SylvainVanIniitu/Piccolo-4C-Black/src/transfoAffichage.h

// void affichage () {}
// sera effacée TODO DEBUG ****

// PROTOTYPE
String GiveNameOfMode(int NNN);
int plusGrandNombreAvecAbits(int a);
String GiveNameOfModeShort(int NNN);

// FC
void affichageLine1()
{

    int potVal2;
    potVal2 = softwareValueEncoderRight;

    switch (Transfo[softwareValueEncoderLeft][0])
    {

        // NOTE**** on peut remplacer quasi tous les printRotFast par un PrintRotFast qui va afficher les noms
        // sauf pour certaines exceptions

    case 14: // CH+Time Info     // ajouter MUTE info
    {

        affiche = String(layerChannel[0] + 1); // attention, le layerChannel n'est pas forcéement le channel de toutes les notes du layer !
        affiche += (F(":"));                   // layerChannel est codé en MIDI hardware : 0 = CHANNEL 1
        affiche += String(layerLength[0]);
        affiche += (F(" "));
        buffer_setCursor(0, 0);
        buffer_print(affiche);

        affiche = String(layerChannel[2] + 1); // attention, le layerChannel n'est pas forcéement le channel de toutes les notes du layer !
        affiche += (F(":"));                   // layerChannel est codé en MIDI hardware : 0 = CHANNEL 1
        affiche += String(layerLength[2]);
        affiche += (F(" "));
        buffer_setCursor(8, 0);
        buffer_print(affiche);

        affiche = String(layerChannel[1] + 1); // attention, le layerChannel n'est pas forcéement le channel de toutes les notes du layer !
        affiche += (F(":"));                   // layerChannel est codé en MIDI hardware : 0 = CHANNEL 1
        affiche += String(layerLength[1]);
        affiche += (F(" "));
        buffer_setCursor(0, 1);
        buffer_print(affiche);

        affiche = String(layerChannel[3] + 1); // attention, le layerChannel n'est pas forcéement le channel de toutes les notes du layer !
        affiche += (F(":"));                   // layerChannel est codé en MIDI hardware : 0 = CHANNEL 1
        affiche += String(layerLength[3]);
        affiche += (F(" "));
        buffer_setCursor(8, 1);
        buffer_print(affiche);
    }
    break;

    case 30:
    { // EYE CANDY
    }
    break;

    case 46: // CH+Ratio Info     // ajouter MUTE info
    {

        affiche = String(layerChannel[0] + 1); // attention, le layerChannel n'est pas forcéement le channel de toutes les notes du layer !
        affiche += (F(":"));                   // layerChannel est codé en MIDI hardware : 0 = CHANNEL 1
        affiche += String(ratioLength[0]);
        affiche += (F(" "));
        buffer_setCursor(0, 0);
        buffer_print(affiche);

        affiche = String(layerChannel[2] + 1); // attention, le layerChannel n'est pas forcéement le channel de toutes les notes du layer !
        affiche += (F(":"));                   // layerChannel est codé en MIDI hardware : 0 = CHANNEL 1
        affiche += String(ratioLength[2]);
        affiche += (F(" "));
        buffer_setCursor(8, 0);
        buffer_print(affiche);

        affiche = String(layerChannel[1] + 1); // attention, le layerChannel n'est pas forcéement le channel de toutes les notes du layer !
        affiche += (F(":"));                   // layerChannel est codé en MIDI hardware : 0 = CHANNEL 1
        affiche += String(ratioLength[1]);
        affiche += (F(" "));
        buffer_setCursor(0, 1);
        buffer_print(affiche);

        affiche = String(layerChannel[3] + 1); // attention, le layerChannel n'est pas forcéement le channel de toutes les notes du layer !
        affiche += (F(":"));                   // layerChannel est codé en MIDI hardware : 0 = CHANNEL 1
        affiche += String(ratioLength[3]);
        affiche += (F(" "));
        buffer_setCursor(8, 1);
        buffer_print(affiche);
    }
    break;



    case 48: // CH+Fidelity Info     //
    {

        affiche = String(layerChannel[0] + 1); // attention, le layerChannel n'est pas forcéement le channel de toutes les notes du layer !
        affiche += (F(":"));                   // layerChannel est codé en MIDI hardware : 0 = CHANNEL 1
        affiche += String(fidelityLayer_[0]);
        affiche += (F(" "));
        buffer_setCursor(0, 0);
        buffer_print(affiche);

        affiche = String(layerChannel[2] + 1); // attention, le layerChannel n'est pas forcéement le channel de toutes les notes du layer !
        affiche += (F(":"));                   // layerChannel est codé en MIDI hardware : 0 = CHANNEL 1
        affiche += String(fidelityLayer_[2]);
        affiche += (F(" "));
        buffer_setCursor(8, 0);
        buffer_print(affiche);

        affiche = String(layerChannel[1] + 1); // attention, le layerChannel n'est pas forcéement le channel de toutes les notes du layer !
        affiche += (F(":"));                   // layerChannel est codé en MIDI hardware : 0 = CHANNEL 1
        affiche += String(fidelityLayer_[1]);
        affiche += (F(" "));
        buffer_setCursor(0, 1);
        buffer_print(affiche);

        affiche = String(layerChannel[3] + 1); // attention, le layerChannel n'est pas forcéement le channel de toutes les notes du layer !
        affiche += (F(":"));                   // layerChannel est codé en MIDI hardware : 0 = CHANNEL 1
        affiche += String(fidelityLayer_[3]);
        affiche += (F(" "));
        buffer_setCursor(8, 1);
        buffer_print(affiche);
    }
    break;

    case 82:
    {
        // TODO DEBUG  à modifier de façon plus jolie !
        currentFileNumber = softwareValueEncoderRight;

        if (SDCardPresente == true)
        {
            NameTransfo = F("Load Nr");
            NameTransfo += String(currentFileNumber);
            printRot2(NameTransfo, 11, 400, 2);
        }
        else
        {
            affiche = "NO SD";
            printRot2(affiche, 11, 400, 2);
        }
    }
    break;

        /* DISMISS 2C27 

    case 84:
    {
        currentFileNumber = softwareValueEncoderRight;

        if (SDCardPresente)
        {
            NameTransfo = F("PLAY MIDI#");
            NameTransfo += String(currentFileNumber);
            printRot2(NameTransfo, 11, 400, 2);
        }
        else
        {
            affiche = "NO SD";
            printRot2(affiche, 11, 400, 2);
        }

        // NameFileNumber(currentFileNumber) ;
        // printRot2(name,10,400,3);
        // midiname = name ;

        // print(F("PLAY MIDI#"));
        // print(currentFileNumber);
        // .print(F("   "));
        // u.setCursor(0, 1);
        // NameFileNumber(currentFileNumber) ;
        // .print(name);
        // midiname = name ;
    }
    break;
*/

    case 93:
    {
        currentFileNumber = softwareValueEncoderRight;

        if (SDCardPresente)
        {
            NameTransfo = F(">LOAD MIDI#");
            NameTransfo += String(currentFileNumber);
            printRot2(NameTransfo, 11, 400, 2);
        }
        else
        {
            printRot2("NO SD", 11, 400, 2);
        }
    }
    break;

    case 111:
    {
        affiche = PiccoloVersion;
        printRot2(affiche, 10, 300, 2);
    }
    break;

    case 126: // Define Which
    {
        switch (Evenement[CurrentEvenement].type)
        {
        case (1):
        {
            printRot2(F("Select CC"), 11, 400, 2);
        }
        break;

        case (2):
        {
            printRot2(F("Select Transfo"), 11, 400, 2);
        }
        break;
        default:
        {
            printRot2(F("Select Type first !"), 11, 400, 2);
        }
        break;
        }
    }
    break;

    case 134:
    {
        // Define Value

        if (Evenement[CurrentEvenement].type == 1)
        {
            printRot2(F(">Select Value to send to CC"), 11, 400, 2);
        }

        if (Evenement[CurrentEvenement].type == 2)
        {
            printRot2(F(">Select Transfo VALUE"), 11, 400, 2);
            // // old potVal2 mapping ;
            // // old potVal2 mapping ;

            // d'abord déterminer quelle est la transfo actuellement envisagée
            // ensuite savoir quelle ligne du tableau Transfo appelle cette Transformation
            // ensuite faire un mapping entre potVal2 et les valeurs données par Transfo !

            // potVal2 = map(potVal2, 0, 1023, Transfo[LineCallingTransfo(Evenement[CurrentEvenement].which)][1], Transfo[LineCallingTransfo(Evenement[CurrentEvenement].which)][2] ) ;

            // dans un premier temps on peut afficher la valeur telle que modifiée par le tableau TRANSFO
            // pour la Transformation[Which]
            // dans second temps il faut viser affichage comme dans le browser habituel

            // String affiche ;
            // affiche = "Send " + String(potVal2) + " to Transfo" + String(Evenement[CurrentEvenement].which) ;
            // printRot2(affiche,10,400,3  );

            // NOTE **** On doit ici compléter par le nom de la transformation
        }
    }
    break;

    case 163:
    { // view Channel direction
        // // old potVal2 mapping ;
        // // old potVal2 mapping ;

        // GetNameTransformation( softwareValueEncoderRight );
        NameTransfo = "CH" + String(potVal2);
        printRot2(NameTransfo, 11, 400, 2);

        //buffer_and_HARD_setCursor(0, 1);
        //printMatrixLine(midiRedirect,potVal2-1);
    }
    break;

    case 246: // layer Counters
    {

        affiche = "1:"; // attention, le layerChannel n'est pas forcéement le channel de toutes les notes du layer !
        affiche += String(layerCounter[0]);
        affiche += (F(" "));
        buffer_setCursor(0, 0);
        buffer_print(affiche);

        affiche = "3:"; // attention, le layerChannel n'est pas forcéement le channel de toutes les notes du layer !
        affiche += String(layerCounter[2]);
        affiche += (F(" "));
        buffer_setCursor(8, 0);
        buffer_print(affiche);

        affiche = "2:"; // attention, le layerChannel n'est pas forcéement le channel de toutes les notes du layer !
        affiche += String(layerCounter[1]);
        affiche += (F(" "));
        buffer_setCursor(0, 1);
        buffer_print(affiche);

        affiche = "4:"; // attention, le layerChannel n'est pas forcéement le channel de toutes les notes du layer !
        affiche += String(layerCounter[3]);
        affiche += (F(" "));
        buffer_setCursor(8, 1);
        buffer_print(affiche);
    }
    break;

    case 373:
    {
        // TODO DEBUG  à modifier de façon plus jolie !
        currentFileNumber = softwareValueEncoderRight;

        if (SDCardPresente == true)
        {
            NameTransfo = F("Load Nr");
            NameTransfo += String(currentFileNumber);
            printRot2(NameTransfo, 11, 400, 2);
        }
        else
        {
            affiche = "NO SD";
            printRot2(affiche, 11, 400, 2);
        }
    }
    break;

    case 508:
    {
        // TODO DEBUG  à modifier de façon plus jolie !
        currentFileNumber = softwareValueEncoderRight;

        if (SDCardPresente == true)
        {
            NameTransfo = F("K_Load Nr");
            NameTransfo += String(currentFileNumber);
            printRot2(NameTransfo, 11, 400, 2);
        }
        else
        {
            affiche = "NO SD";
            printRot2(affiche, 11, 400, 2);
        }
    }
    break;

    default:
    {
        GetNameTransformation(Transfo[softwareValueEncoderLeft][0]);
        printRot2(NameTransfo, 12, 400, 2);
    }
    break;

    } // end of switch avec toutes les valeurs de Transformatiosn

} // fin de la procédure affichage Line 1

void affichageLine2(int thisTransfo)
{
    int potVal2;
    potVal2 = softwareValueEncoderRight;

    busyWithMIDIAffichage = false; // il faut veiller qd on sort de 218 à passer au moins 1x par l'affichage de 217
    // pour toutes les fois où on n'est pas dans 218, fait que cette valeur est fausse
    // NOTE DEBUG je n'ai pas trouvé de moyen plus court pour dire qd on n'est pas dans une fc qui rend cette valeur vraie
    //
    // switch ( Transfo[softwareValueEncoderLeft][0] ) {
    switch (thisTransfo)
    {
        // NOTE**** on peut remplacer quasi tous les printRotFast par un PrintRotFast qui va afficher les noms
        // sauf pour certaines exceptions

    case 6:
    {
        // potVal2 = analogRead(A1);

        switch (potVal2)
        {
        case 1:
            potVal2 = 1;
            break;
        case 2:
            potVal2 = 10;
            break;
        case 3:
            potVal2 = 100;
            break;
        case 4:
            potVal2 = 1000;
            break;
        case 5:
            potVal2 = 10000; // soit 10 secondes            break;
        }

        String affiche;
        affiche = String(potVal2) + F(" msec ");
        printRot2(affiche, 16, 400, 3);
    }
    break;

    case 11:
    { // MULTIPLY

        int potVal3 = (softwareValueEncoderRight / 7) + 1;
        potVal2 = (softwareValueEncoderRight % 7) + 1;

        String affiche;
        affiche = String(potVal2) + F("/") + String(potVal3) + F(" ");
        printRot2(affiche, 16, 400, 3);
    }
    break;

    case 12:
    { // Meltiply

        int potVal3 = (softwareValueEncoderRight / 7) + 1;
        potVal2 = (softwareValueEncoderRight % 7) + 1;

        String affiche;
        affiche = String(potVal2) + F("/") + String(potVal3) + F(" ");
        printRot2(affiche, 16, 400, 3);
    }
    break;

    case 14: // CH+Time Info     // ajouter MUTE info
    {
    }
    break;

    case 20:
    {
        // printRotFast(F("(un)MUTE"));
        //
        // TODO transformer en String et PrintRot2 ****

        affiche = nulString;
        ;
        for (byte i = 0; i < nbLayer; i++)
        {
            // déterminer si la layer i est mute
            // déterminer si la layer i est mute
            byte k = ((muteLayer >> i) & B00000001); // le bit de droite est 1 si layer 0 est MUTE ; le 2ème bit est 1 si layer 1 est MUTE, etc...
            if (k == B00000001)
            {
                affiche += F("M");
            }
            else
            {
                affiche += (F("-"));
            }
        }
        printRot2(affiche, 16, 300, 3);
    };
    break;

    case 23:
    { // AUTO FX

        affiche = nulString;
        if (automodification == true)
        {
            affiche = F(" ON ");
        }
        else
        {
            affiche = F("OFF");
        }

  
        // // old potVal2 mapping ;
        // potVal2 = map(potVal2, 0, 1023, Transfo[softwareValueEncoderLeft][1] , Transfo[softwareValueEncoderLeft][2] + 1); // dépendra de l'effet choisi.

        affiche = affiche + String(potVal2) + F(" sec");
        printRot2(affiche, 16, 400, 3);
    }

    break;

    case 24:
    { // RECORD ON/OFF
        printRot2(record == true ? F("ON ") : F("OFF"), 16, 300, 3);
    }
    break;

    case 25: // MIDIOx MIDI Ox
    {

        // MODIF 2C18 KANNIBAL 2 !!!
        // on enlève le .Read direct, pour se fier à la dernière valeur enrgistrée !
        // 2C19 on enlève l'affichage F8 !

        // byte note(0);
        // byte channel(0);
        // byte velocity(0);
        // String affiche;

        // if (MIDI3.read(0))
        // {
        //     channel = MIDI3.getChannel(); // donne le channel, pas le codage du channel ! CH1 = 0 pour machine
        //     note = MIDI3.getData1();
        //     velocity = MIDI3.getData2();
        //     timenote = nowMillis;
        // }

        // if ( note != 0 ) {
        switch (midiType)
        {
        case midi::NoteOn:
        {
            // digitalWrite(5, HIGH);

            affiche = F("CH");
            affiche += String(channel + 1); //2C28 affichage toujours humain, calculs toujours machine
            affiche = affiche + F("N");
            affiche = affiche + String(note);
            affiche = affiche + ".";
            affiche = affiche + String(velocity);
            printRot2(affiche, 16, 400, 3);

            //  digitalWrite(5, LOW);
        }
        break;

        case midi::NoteOff:
        {
            affiche = F("CH");
            affiche += String(channel + 1); // 2C28 affichage toujours humain, calcul toujours machine
            affiche = affiche + F("N");
            affiche = affiche + String(note);
            affiche = affiche + F("x");
            affiche = affiche + String(velocity);
            printRot2(affiche, 16, 400, 3);
        }
        break;

            // polyPressure            = 0x0A,
            //   56         controlChange           = 0x0B,
            //   57         programChange           = 0x0C,
            //   58         channelPressure         = 0x0D,
            //   59         pitchBend               = 0x0E,
            //
            //

        case midi::AfterTouchPoly:
        {
            affiche = F("PolyPressureCH");
            affiche += String(channel + 1);
            affiche = affiche + F("N");
            affiche = affiche + String(note);
            affiche = affiche + F(":");
            affiche = affiche + String(velocity);
            printRot2(affiche, 16, 400, 3);
        }
        break;

        case midi::ControlChange:
        {
            // if (channel != 0 && note != 0)
            if (note != 0)
            {
                affiche = F("/CC/ CH");
                affiche += String(channel + 1);
                affiche = affiche + F("V");
                affiche = affiche + String(note);
                affiche = affiche + F(":");
                affiche = affiche + String(velocity);
                affiche += F(" ");
                printRot2(affiche, 16, 400, 3);
            }
        }
        break;

        case midi::ProgramChange:
        {
            affiche = F("*PC* CH");
            affiche += String(channel + 1);
            affiche = affiche + F("V");
            affiche = affiche + String(note);
            affiche = affiche + F(":");
            affiche = affiche + String(velocity);
            printRot2(affiche, 16, 400, 3);
        }
        break;

        case midi::PitchBend:
        {
            affiche = F("Bend CH");
            affiche += String(channel + 1);
            affiche = affiche + F("V");
            affiche = affiche + String(note);
            affiche = affiche + F(":");
            affiche = affiche + String(velocity);
            printRot2(affiche, 16, 400, 3);
        }
        break;

        default:
            if (midiType != 248)
            {
                affiche = String(midiType);
                affiche += "/";
                affiche += String(channel + 1);
                affiche = affiche + F("?");
                affiche = affiche + String(note);
                affiche = affiche + F("?");
                affiche = affiche + String(velocity);
                printRot2(affiche, 16, 400, 3);

                break;
            }
        }
        // }
    }
    break;

    case 26:
    {
        // premier de la deuxième ligne à bénéficier de printRot2

        // String affiche ;
        affiche = "1 iter = ";
        affiche += String((int)currentCounterSpeed);
        // affiche += "->";
        // affiche += String((int)meancounterspeed);
        // affiche = affiche + F(" microsec  ");
        //  Rfirsttime[3] = true ; // va forcer l'affichage mis à jour
        printRot2(affiche, 16, 400, 3);
    }
    break;

    case 30:
    { // EYE CANDY
        // buffer_and_HARD_setCursor(random(0, 16), random(0, 2));
        // buffer_and_HARD_print((char)random(33, 255));
        // montrer particulièrement la lenteur d'un écran !!!
    }
    break;

    case 31:
    { // ACTIVE LAYER CHOOSER

        affiche = nulString;

        for (byte i = 0; i < nbLayer; i++)
        {
            // déterminer si la layer i est active
            byte k = ((((byte)potVal2) >> i) & B00000001); // le bit de droite est 1 si layer 0 est ON ; le 2ème bit est 1 si layer 1 est ON, etc...
            if (k == B00000001)
            {
                affiche += String(i + 1);
            }
            else
            {
                affiche += "-";
            }
        }

        printRot2(affiche, 16, 400, 3);
    }
    break;

        /////////////////////////////////////////////////////////////////////////////////////
        // PILE VERSION : faite et vérifiée
        // 1C94
        /////////////////////////////////////////////////////////////////////////////////////

    case 32:
    {
        // FIRST FREEnote

        affiche = nulString;
        ;

        for (byte i = 0; i < nbLayer; i++)
        {
            affiche += String(mesureTaillePileComplete(pInitial[i]));
            // if (anyFreeNote(i))
            // {
            //     affiche += String(firstfreenote(i));
            // }
            // else
            // {
            //     affiche += F("R");
            // }
            affiche += F(".");
        }

        printRot2(affiche, 16, 400, 3);
    };
    break;

    case 35:
    {
        // MIRROR
        // va devoir indiquer le nb de notes présentes avant ce % là des layers

        affiche = nulString;
        affiche += String(potVal2);
        affiche += F("% = ");

        unsigned long foldtime;
        long calcultime; // doit parfois être négatif !!!!
        int total = 0;

        for (byte i = 0; i < nbLayer; i++)
        {

            if (isLayerActive(i))
            {

                calcultime = (((long)layerLength[i] * (long)potVal2) / (long)100);
                foldtime = (signed int)(calcultime);
                // on doit pouvoir se passer de la variable foldtime en fait !
                // affiche+=String(foldtime);

                //1C97
                unsigned int taille = mesureTaillePileComplete(pInitial[i]);
                pileNote tempNote;

                for (byte j = 0; j < taille; j++)
                { //
                    tempNote = ZEROgetNoteFromPile(pInitial[i], j);

                    if ((tempNote.note != 0) && (tempNote.startNote < foldtime))
                    {
                        total++;
                    }
                }
            }
        }

        affiche += String(total);
        affiche += F(" notes");

        printRot2(affiche, 16, 400, 3);
    };
    break;

    case 39:
    { // Velocity

        if (potVal2 < 127)
        {
            affiche = String(potVal2) + " ";
        }
        else
        {
            affiche = F("RND");
        }
        printRot2(affiche, 16, 400, 3);
    }
    break;

    case 40: // HARMONIZE
    {
        //2C19 modification radicale : gamme pour chaque layer

        affiche = nulString;
        // 2C12 va afficher le gamme du layer 1 et transforme tout d'un coup

        // 2C28 : va de C à C et plus de C à F comme avant !

        for (byte i = 0; i < nbLayer; i++)
        {
            if (isLayerActive(i))
            {
                affiche += GiveNameOfNote(potVal2);
                affiche += " ";
            }
            else
            {
                affiche += (GiveNameOfNote(gammeActuelle[i]));
                affiche += " ";
            }
        }

        printRot2(affiche, 16, 400, 3);
    }
    break;

    case 41: // ROOT NOTE
    {
        // 2C12 va afficher le gamme du layer 1 et transforme tout d'un coup

        // 2C27
        affiche = GiveNameOfNote(potVal2);
        affiche += flechedroite;

        for (byte i = 0; i < nbLayer; i++)
        {
            // if (isLayerActive(i))
            //  {
            //     affiche += GiveNameOfNote(potVal2);
            //     affiche += " ";
            // }
            // else
            {
                affiche += (GiveNameOfNote(gammeActuelle[i]));
                affiche += " ";
            }
        }

        printRot2(affiche, 16, 400, 3);
    }
    break;

    case 42:
    { // affichage du Record MODE
        affiche = nulString;
        ;

        // potVal2 = analogRead(A1);
        // old potVal2 mapping ;
        // old potVal2 mapping ;

        switch (potVal2)
        {
        case 0:
            affiche += (F("1.REC 2 LAYER CH"));
            break;
        case 1:
            affiche += (F("2.REC + SOURCE CH"));
            break; // par défaut
        case 2:
            affiche += (F("3.REC - CH        "));
            break;
        default:
            affiche += (F("oink"));
            break;
        }
        printRot2(affiche, 16, 400, 3);
    }
    break;

    case 45:
    {
        // old potVal2 mapping ;
        // old potVal2 mapping ;

        affiche = nulString;

        affiche = String(potVal2);
        affiche += F("%  ");

        // TODO fonction qui remplace ceci : va combler String jusque 8

        switch (varispeedState)
        {
        case 1:
            affiche += (F("  OFF"));
            break;
        case 2:
        {
            affiche += (F("  ON!"));

            for (byte i = 0; i < nbLayer; i++)
            {
                if (isLayerActive(i))
                {
                    ratioCurrent[i] = potVal2; //
                }
            }
        }
        break;
        case 3:
            affiche += (F("  FIX"));
            break;
        case 4:
            affiche += (F("  MOD"));
            break;
        default:
            affiche += (F("  ???"));
            break;
        }
        printRot2(affiche, 16, 400, 3);
    }
    break;

    case 46:
    { // CH+Ratio Info     // ajouter MUTE info
    }
    break;

    case 47: // Fidelity Black10
    {
affiche = nulString ; 
// affiche += potVal2 ;
affiche += afficheValueStraightOrFromSequence(potVal2, "%", 0);
affiche += ">"; 

        for (byte i = 0; i < nbLayer; i++)
        {
            affiche += afficheValueStraightOrFromSequence(fidelityLayer_[i], "%", 0);
            affiche += " "; 
        }
        printRot2(affiche, 16, 400, 3);
      }
    break;

    case 48:
    { // CH+Fidelity Info     //
    }
    break;

    case 50: // Tabula Rasa
    {

        affiche = nulString;
        ;

        // potVal2 = analogRead(A1);
        // old potVal2 mapping ;
        // old potVal2 mapping ;

        switch (potVal2)
        {
        case 0:
            affiche += (F("0??      "));
            break;
        case 1:
            affiche += (F("Pyramid  "));
            break;
        case 2:
            affiche += (F("Square   "));
            break;
        case 3:
            affiche += (F("Random   "));
            break;
        case 4:
            affiche += (F("Complex  "));
            break;
        case 5:
            affiche += (F("Long 32  "));
            break;
        case 6:
            affiche += (F("SlaveRave"));
            break;
        case 7:
            affiche += (F("Technoid4"));
            break;
        case 8:
            affiche += (F("5/5/3   "));
            break;
        case 9:
            affiche += (F("3/5/3    "));
            break;
        default:
            affiche += (F("--------- "));
            break;
        }
        printRot2(affiche, 16, 400, 3);
    };
    break;

    case 51:
    {

        affiche = nulString;
        ;

        //        potVal2 = analogRead(A1);
        // old potVal2 mapping ;
        // old potVal2 mapping ;
        if (potVal2 < 17)
        {
            affiche = String(potVal2); // le CH MIDI est la valeur +1
        }
        else
        {
            switch (potVal2)
            {
            case 17:
                affiche = F("idem");
            case 18:
                affiche = F("OFF ");
            default:
                break;
            }
        }
        printRot2(affiche, 16, 400, 3);
    };
    break;

    case 58:
    { // FUNKY VEL   FunkyVel FunkyVelValue
        affiche = nulString;

        affiche = String(potVal2);
        affiche += F(" ");

        if (FunkyVel == true)
        {
            affiche += (F("ON  "));
        }
        else
        {
            affiche += (F("OFF "));
        }

        for (byte i = 0; i < nbLayer; i++)
        {
            affiche += String(FunkyVelValue[i]);
            affiche += " ";
        }

        printRot2(affiche, 16, 400, 3);
    }
    break;

    case 63:
    { // REP FRACT TODO DEBUG ne marche pas je crois

        affiche = nulString;

        int potVal3 = (softwareValueEncoderRight / 16) + 1;
        potVal2 = (softwareValueEncoderRight % 16) + 1;

        affiche = F("1+");
        affiche += String(potVal2);
        affiche += (F("/"));
        affiche += String(potVal3);
        affiche += (F("    "));

        printRot2(affiche, 16, 400, 3);
    }
    break;

    case 82:
    {
        // DEBUG TODO **** pas clair ce qui doit figurer en ligne 1 et ligne 2
        // surtout pour l'event Transfo

        currentFileNumber = softwareValueEncoderRight;

        affiche = nulString;

        affiche = String(currentFileNumber);
        affiche += F(".");
        NameFileNumber(currentFileNumber);
        affiche += name;

        printRot2(affiche, 16, 400, 3);
    }
    break;

    case 83:
    {
        printRot2(Daubymodification == true ? F("ON ") : F("OFF"), 16, 300, 3);
    }

    break;

    case 84:
    {
        currentFileNumber = softwareValueEncoderRight;

        affiche = nulString;
        ;

        affiche = String(currentFileNumber);
        affiche += F(".");
        NameFileNumber(currentFileNumber);
        affiche += name;

        printRot2(affiche, 16, 400, 3);
        midiname = name;

        // NameFileNumber(currentFileNumber) ;
        // midiname = name ;
    }
    break;

    case 87:
    {
        // Transfo[LineCallingTransfo(87)][2] = (unsigned int) tailleTotaleMIDI;    // première fois qu'une valeur du tableau est modifié à posteriori, en fc de taille du fichier.
        // DEBUG NOTE pas beau, à modifier !
    }
    break;

    case 93:
        // s'inspirer de 373
        {

            currentFileNumber = softwareValueEncoderRight;
            maximumSoftwareValueEncoderRight = rootFileCount;

            affiche = nulString;

            affiche = String(currentFileNumber);
            affiche += F(".");

            if (oldNumber != currentFileNumber)
            {
                NameFileNumber(currentFileNumber);
            }

            oldNumber = currentFileNumber;
            affiche += name;

            printRot2(affiche, 16, 400, 3);
            fileName = name;

            // midiname = name ;
            // TODO : restreindre la lecture au fichier .mid ?
        }
        break;

    case 94:
    {
        printRot2(SqueezeOn == true ? F("ON ") : F("OFF"), 16, 300, 3);
    }
    break;

    case 95:
    {
        printRot2(KeepLength == true ? F("ON ") : F("OFF"), 16, 300, 3);
    }
    break;

    case 97:
    {
        affiche = nulString;
        ;

        affiche = ("(");
        affiche += String(kNecklace);
        affiche += (F(","));
        affiche += String(mNecklace);
        affiche += (F(") - # "));
        affiche += String(NoteNecklace);
        affiche += (" Sh");
        affiche += String(ShiftNecklace);

        printRot2(affiche, 16, 400, 3);
    }
    break;

    case 106:
    {
        // old potVal2 mapping ;
        // old potVal2 mapping ;
        affiche = nulString;

        MultiplicationsString = GatedString(potVal2, NbMultiplications);
        affiche = MultiplicationsString;
        printRot2(affiche, 16, 400, 3);
        // attention dans ce cas-ci c'est MultiplicationsString qui passe l'info au Transfo, pas PotVal3
        // DEBUG pourquoi ceci ? parce que MultiplicationString est constitué à partir de 2 infos : du 106 et 107
        // on pourrait néanmoins passer les 2 infos.
        // DEBUG Gated Mutliple est typiquement une transfo qui gagnerait à faire l'objet d'un multiple OK
    }
    break;

    case 107:
    {

        // old potVal2 mapping ;
        // old potVal2 mapping ;

        affiche = nulString;
        ;

        affiche = String(potVal2);
        affiche += F(" fois");
        printRot2(affiche, 16, 400, 3);
        // potVal2 = analogRead(A1);

        // Si on fait clic, la transfo 107 va faire  :
        // NbMultiplications = potVal3 ;
        // Transfo[LineCallingTransfo(106)][2] = MaximumBinForSteps(NbMultiplications);
        // et donc la fonction 106 est armée pour créer le GatedString
    }
    break;

    // Transfo[SizeTransfo][4]
    case 108:
    {
        // Vertical Mapping
        affiche = nulString;
        ;

        affiche = (F("("));

        affiche += String(FindLowestNoteOfActive());
        affiche += (F(","));

        affiche += String(FindHighestNoteOfActive());
        affiche += (F(")"));
        affiche += flechedroite;
        affiche += F("(");
        // TODO flèche : (String) ((char)(B01111110) );

        // TODO DEBUG problème qd ceci est affiché appelé par Event : ne sera pas juste !
        //
        affiche += String(Transfo[LineCallingTransfo(108)][1]);
        affiche += (F(","));
        affiche += String(Transfo[LineCallingTransfo(108)][2]);
        affiche += (F(")"));
        printRot2(affiche, 16, 400, 3);
    }
    break;

    case 111:
    {

        affiche = PiccoloDate;
        printRot2(affiche, 16, 300, 3);
    }
    break;

    case 112:
    {
        printRot2(autoHarmonize == true ? F("ON ") : F("OFF"), 16, 300, 3);
        // modèle à appliquer à d'autres exemples plus haut !
    }
    break;

    case 113:
    {
        printRot2(complexSqueeze == true ? F("ON ") : F("OFF"), 16, 300, 3);
    }
    break;

    case 114:
    {
        affiche = nulString;
        ;

        // potVal2 = analogRead(A1);
        // old potVal2 mapping ;
        // old potVal2 mapping ;

        switch (potVal2)
        {
        case 0:
            affiche = (F("1.0??      "));
            break;
        case 1:
            affiche = (F("1.Delete "));
            break;
        case 2:
            affiche = (F("2.Wrap  "));
            break;
        case 3:
            affiche = (F("3.Limit "));
            break;
        case 4:
            affiche = (F("4.Bounce "));
            break;
        default:
            affiche = (F("6.--------- "));
            break;
        }
        printRot2(affiche, 16, 400, 3);
    }
    break;

    case 115:
    {
        affiche = nulString;

        affiche = (playParallelMidiON == true ? F("ON ") : F("OFF"));
        affiche += F("  f:"); // pour file
        affiche += (midiname);

        printRot2(affiche, 16, 400, 3);

        // 2C28 progress
        affiche = "[";
        affiche += String(midiFile_progress);
        affiche += "/";
        affiche += String(midiFile_totalNotes);
        affiche += "]";

        // buffer_and_HARD_setCursor() : le modifie aussi en hardware pour l'écran
        buffer_setCursor(0, 6);
        buffer_print(affiche);
    }
    break;

    case 116:
    {
        affiche = nulString;

        // old potVal2 mapping ;
        // old potVal2 mapping ;

        switch (potVal2)
        {
        case 1:
            affiche = (F("1.Bounce Even"));
            break;
        case 2:
            affiche = (F("2.Bounce ALL"));
            break;
        case 3:
            affiche = (F("3.UK"));
            break;
        case 5:
            affiche = (F("4.UK"));
            break;
        case 6:
            affiche = (F("5.UK"));
            break;
        default:
            affiche = (F("6.UK "));
            break;
        }
        printRot2(affiche, 16, 400, 3);
    }
    break;

    case 119:
    { // Phasage

        affiche = nulString;
        ;
        // affiche = afficheRatio(potVal2, 32, 32, true); // le true indique ici que les valeurs peuvent être négatives
        affiche = String(potVal2);
        affiche += "/";
        affiche += String(nPhasage);
        printRot2(affiche, 16, 400, 3);
    }
    break;

    case 120:
    { // Phasage

        affiche = nulString;
        ;
        // affiche = afficheRatio(potVal2, 32, 32, true); // le true indique ici que les valeurs peuvent être négatives
        affiche = String(kPhasage);
        affiche += "/";
        affiche += String(potVal2);
        printRot2(affiche, 16, 400, 3);
    }
    break;

    case 121:
        // ROTATE
        {
            affiche = nulString;
            ;

            affiche = String(potVal2);
            affiche += F(" [x:");
            affiche += String(CentreX);
            affiche += F(",y:");
            affiche += String(CentreY);
            affiche += F("]");

            printRot2(affiche, 16, 400, 3);
        }
        break;

    // case 122: break ; // printRot2 (F("> Set x (longueur layer)") ); break; // TODO
    // case 123: break ; // printRot2 (F("> Set y (pitch)") ); break;
    case 124:
        break; // printRot2(F("Affichage (x,y)") ); break;  // NOTE**** à combiner avec 121

    case 125:
    { // Activate Event

        affiche = nulString;

        affiche = (Evenement[potVal2].actif == true ? F("ON ") : F("OFF"));
        affiche += " ";
        affiche += giveStringOfEvent(potVal2);
        printRot2(affiche, 16, 300, 3);

        // affiche =  nulString ; ;
        //
        // affiche = String (CurrentEvenement);
        // printRot2(affiche  ,16,400,3);

        // NOTE **** faire un String avec tout ceci pour récapituler
        // Evenement[i].type = 1 ; // 0 = vide  1=CC 2=Transfo
        // // pour les Transfo modifiant valeur, elle devront voir le type défini
        // Evenement[i].intervalle  = 150  ; // 1 = 0.1sec
        // Evenement[i].moment = 50 ; // dans les temps divisible par 300, agit après 100
        // Evenement[i].fidelite  = 100  ; // %
        // Evenement[i].which  =  17 ; // définit quel CC va être modifié
        // Evenement[i].valeur  = 55  ; // définit la valeur initiale qui lui sera attribuée
        // Evenement[i].shape   = 4  ; // 1=fixe 2=inc 3=Dec 4=rnd 5=liste
        // Evenement[i].rangeUP  = 100  ;
        // Evenement[i].rangeLO  = 10  ;
        // Evenement[i].incSize  = 0  ;
        // Evenement[i].behaviorLimit  = 0  ;
        // Evenement[i].channel  = 5 ; // à supposer que la machine recevant le CC soit en midi 5 (CH6)
        // Evenement[i].layer  = 0  ;   // tous layers actives - non pertinent pour un CC, car ne modifie pas de layers !
        // Evenement[i].eventGOON = millis() - ( millis() % Evenement[i].intervalle ) + Evenement[i].intervalle + Evenement[i].moment ;
        //
    }
    break;

    case 126:
    { // Define Which
        affiche = nulString;
        ;
        // affiche = F( "Evt") ;
        // affiche += String(CurrentEvenement);
        affiche = giveStringOfEvent(CurrentEvenement);

        switch (Evenement[CurrentEvenement].type)
        {
        case (1):
        {
            // old potVal2 mapping ;
            // old potVal2 mapping ;

            affiche += (F(" CC"));
            affiche += String(potVal2);
        }
        break;
        case (2):
        {
            // old potVal2 mapping ;
            // potVal2 = map(potVal2, 0, 1023, 0, SizeTransfo ) ;

            // GetNameTransformation(potVal2,1); // 1 c'est le mode où on a un chiffre devant !
            GetNameTransformation(Transfo[potVal2][0], 1); // 1 c'est le mode où on a un chiffre devant !
            // TODO il faudra changer le chiffre attribué par GetNameTransformation
            //
            affiche += " ";
            affiche += NameTransfo;
            // NOTE **** on doit adapter le printRotFast pour plusieurs lieux
        }
        break;
        default:
        {
            affiche += F(" ouin?");
        }
        break;
        }
        printRot2(affiche, 16, 400, 3);
    }
    break;

    case 127:
    {
        // old potVal2 mapping ;
        // old potVal2 mapping ;

        affiche = nulString;
        ;
        affiche = giveStringOfEvent(CurrentEvenement);
        affiche += (F(" <- "));
        affiche += String(potVal2 + 1);
        printRot2(affiche, 16, 400, 3);
    }
    break;

    case 128:
    { // Delete Event
        affiche = nulString;
        affiche = giveStringOfEvent(CurrentEvenement);

        printRot2(affiche, 16, 400, 3);

        // NOTE **** on pourra adapter plus tard si on veut choisir quel Event Effacer sans d'abord devoir le sélectionner
    }
    break;

    case 129:
    { // Define Type
        // old potVal2 mapping ;
        // old potVal2 mapping ;
        affiche = nulString;
        ;
        affiche = giveStringOfEvent(CurrentEvenement);
        switch (potVal2)
        {
        case 0:
            affiche += (F(" 0.--"));
            break;
        case 1:
            affiche += (F(" 1.CC"));
            break;
        case 2:
            affiche += (F(" 2.Tf/Value"));
            break;
        default:
            affiche += (F(" Ugh?"));
            break;
        }
        printRot2(affiche, 16, 400, 3);
    }
    break;

    case 130:
    {
        // Define Intervalle
        // old potVal2 mapping ;
        affiche = nulString;

        if (Evenement[CurrentEvenement].typeInterval == 4)
        {
            affiche = "NOT FOR MODULO";
        }
        else
        {

            affiche = giveStringOfEvent(CurrentEvenement);

            // old potVal2 mapping ;

            affiche += String((float)potVal2 / (float)10); // on divise par 10 car on exprimera en secondes
            affiche += (" sec");
        }
        printRot2(affiche, 16, 400, 3);
    }
    break;

    case 131:
    { // Define Moment
        affiche = nulString;

        if (Evenement[CurrentEvenement].typeInterval == 4)
        {
            affiche = "NOT FOR MODULO";
        }
        else
        {

            affiche = giveStringOfEvent(CurrentEvenement);
            // Transfo[131][2]=(int) Evenement[CurrentEvenement].intervalle ;
            // 3 semaines pour trouver ce BUG !!!
            // c'était bien une mauvaise idée de faire transformer des valeurs du tableau !
            Transfo[LineCallingTransfo(131)][2] = (int)Evenement[CurrentEvenement].intervalle;
            // DEBUG NOTE à modifier !!!!

            // old potVal2 mapping ;
            // old potVal2 mapping ;

            affiche += String((float)potVal2 / (float)10); // on divise par 10 car on exprimera en secondes
            affiche += (" sec");
        }
        printRot2(affiche, 16, 400, 3);
    }
    break;

        // TODO DEBUG il y a une confusion dans rangeLO et rangeUP pour 'lintervalle '
        // et pour les valeurs de la transformation ou du CC
        // il faut éclaircir tout cela

    case 132:
    { // Define Fidelité Event
        affiche = nulString;
        ;
        affiche = giveStringOfEvent(CurrentEvenement);

        affiche += String(potVal2); // on divise par 10 car on exprimera en secondes
        affiche += (" %");
        printRot2(affiche, 16, 400, 3);
    }
    break;

    case 133:
    { // Define Type Intevalle
        // old potVal2 mapping ;
        // old potVal2 mapping ;

        // byte typeInterval ; // 1 = constant 2 = random(a,b)  3=gaussian   4 = bi intervalle
        // NOTE **** à implémenter
        // Si 1 : OK pour .intervalle et .moment
        // Si 2 : valeur Min, valeur Max : Valeur Max = Intervalle , Valeur Min = Moment
        // Si 3 : Valeur Min = distrib 0 ; Valeur max = distrib totale
        // Si 4 : bof
        //
        //
        affiche = nulString;
        affiche = giveStringOfEvent(CurrentEvenement);

        switch (potVal2)
        {
        case 1:
        {
            affiche += (F(" 1.Const spc"));
        }
        break;
        case 2:
        {
            affiche += (F(" 2.Rnd spc("));
            affiche += String(Evenement[CurrentEvenement].rangeLO_);
            affiche += (F(","));
            affiche += String(Evenement[CurrentEvenement].rangeUP_);
            affiche += (F(")"));
        }
        break;
        case 3:
        {
            affiche += (F(" 3.Gauss spc("));
            affiche += String(Evenement[CurrentEvenement].rangeLO_);
            affiche += (F(","));
            affiche += String(Evenement[CurrentEvenement].rangeUP_);
            affiche += (F(")"));
        }
        break;
        case 4:
        {
            affiche += (F(" 4.MODULO"));
        }
        break;

        default:
            affiche += (F(" Ugh?"));
            break;
        }
        printRot2(affiche, 16, 400, 3);
    }
    break;

    case 134:
    {
        // Define Value
        affiche = nulString;
        affiche = giveStringOfEvent(CurrentEvenement);

        if (Evenement[CurrentEvenement].type == 1)
        {
            // old potVal2 mapping ;
            // old potVal2 mapping ;

            affiche += F(" Send");
            affiche += String(potVal2);
            affiche += F(" to CC");
            affiche += String(Evenement[CurrentEvenement].which);
            printRot2(affiche, 16, 400, 3);
        }
        else if (Evenement[CurrentEvenement].type == 2)
        {
            // // old potVal2 mapping ;
            // // old potVal2 mapping ;

            // d'abord déterminer quelle est la transfo actuellement envisagée
            // ensuite savoir quelle ligne du tableau Transfo appelle cette Transformation
            // ensuite faire un mapping entre potVal2 et les valeurs données par Transfo !

            // potVal2 = map(potVal2, 0, 1023, Transfo[LineCallingTransfo(Evenement[CurrentEvenement].which)][1], Transfo[LineCallingTransfo(Evenement[CurrentEvenement].which)][2] ) ;

            //affichageLine2(softwareValueEncoderRight) ;
            // DEBUG faux on doit indiquer la transformation, pas la valeur !

            affichageLine2(Evenement[CurrentEvenement].which);

            // TODO je crois qu'on doit faire de même pour LO et HI !!! on doit afficher ce que cela vaut pour la transformation donnée

            // dans un premier temps on peut afficher la valeur telle que modifiée par le tableau TRANSFO
            // pour la Transformation[Which]
            // dans second temps il faut viser affichage comme dans le browser habituel

            // affiche =  nulString ;
            // affiche += F("Send ") ;
            // affiche += String(potVal2) ;
            // affiche += F( " to Transfo") ;
            // affiche += String(Evenement[CurrentEvenement].which) ;
            // printRot2(affiche,16,400,3  );

            // NOTE **** On doit ici compléter par le nom de la transformation
        }
        else
        {
            String affiche;
            affiche += F(" Define type first");

            printRot2(affiche, 16, 400, 3);
        }
    }
    break;

    case 135:
    {
        // Define Type
        // old potVal2 mapping ;
        // old potVal2 mapping ;

        // 135 DEFINE SHAPE
        // byte shape ;  // 1 = valeur fixe ( pour valeur )
        // 2 = INC
        // 3 = DEC ( ou bien INC avec valeur négative ? )
        // 4 = RND  ( définir min et max, 0-127 par défaut pour CC )
        // 5 = LISTE : ex 4 valeurs 37,69,120,130
        //  5=liste sequential 6 = liste random
        // // NOTE**** il faudra pour la liste réapprendre les pointeurs; j'en aurai de toutes façons besoins pour passer
        // des fragments (bars) à des morceaux.
        //
        affiche = nulString;
        ;
        affiche = giveStringOfEvent(CurrentEvenement);

        switch (potVal2)
        {
        case 1:
            affiche += (F(" 1.ct val"));
            break;
        case 2:
            affiche += (F(" 2.inc val ("));
            affiche += (Evenement[CurrentEvenement].incSize);
            affiche += (F(")"));
            break;
        case 3:
            affiche += (F(" 3.dec val ("));
            affiche += (Evenement[CurrentEvenement].incSize);
            affiche += (F(")"));
            break;
        case 4:
            affiche += (F(" 4.rnd val ("));
            affiche += (Evenement[CurrentEvenement].rangeLO_);
            affiche += (F(","));
            affiche += (Evenement[CurrentEvenement].rangeUP_);
            affiche += (F(")"));
            break;
        case 5:
            affiche += (F(" 5.seq val"));
            break;
        default:
            affiche += (F(" Ugh?"));
            break;
        }
        printRot2(affiche, 16, 400, 3);
    }
    break;

    case 136:
    { // SET RANGE UP

        if (Evenement[CurrentEvenement].type == 1)
        {
            String affiche;
            affiche = giveStringOfEvent(CurrentEvenement);

            affiche += F("Max ");
            affiche += String(potVal2);
            affiche += F(" to CC");
            affiche += String(Evenement[CurrentEvenement].which);
            printRot2(affiche, 16, 400, 3);
        }

        if (Evenement[CurrentEvenement].type == 2)
        {
            affichageLine2(Evenement[CurrentEvenement].which);
        }
    }
    break;

    case 137:
    { // SET RANGE LO

        if (Evenement[CurrentEvenement].type == 1)
        {
            String affiche;
            affiche = giveStringOfEvent(CurrentEvenement);

            affiche += F("Min ");
            affiche += String(potVal2);
            affiche += F(" to CC");
            affiche += String(Evenement[CurrentEvenement].which);
            printRot2(affiche, 16, 400, 3);
        }

        if (Evenement[CurrentEvenement].type == 2)
        {
            affichageLine2(Evenement[CurrentEvenement].which);
        }
    }
    break;

    case 139:
    { // Define behavior at the Limit
        // old potVal2 mapping ;
        // old potVal2 mapping ;
        // 139 DEFINE behaviorLimit
        // byte behaviorLimit ; // pour options shape 2,3
        // 1 = Change direction
        // 2 = qd dépasse vers haut ou bas, réapparait de l'autre côté
        // 3 = reste à la limite
        affiche = nulString;
        affiche = giveStringOfEvent(CurrentEvenement);

        switch (potVal2)
        {
        case 1:
            affiche += (F("1.Inversion"));
            break;
        case 2:
            affiche += (F("2.Worm"));
            break;
        case 3:
            affiche += (F("3.Limit"));
            break;
        default:
            affiche += (F("Ugh?"));
            break;
        }
        printRot2(affiche, 16, 400, 3);
    }
    break;

    case 140:
    {

        affiche = nulString;
        affiche = giveStringOfEvent(CurrentEvenement);

        affiche += " CH";

        affiche += String(potVal2);

        printRot2(affiche, 16, 300, 3);
    }
    break;

    case 141:
    { // Define Layers

        // old potVal2 mapping ;
        // old potVal2 mapping ;

        // NOTE **** problème pour sélectionner ACTIVE LAYERS

        affiche = nulString;
        affiche = giveStringOfEvent(CurrentEvenement);

        affiche += " ";

        if (potVal2 >= 16)
        {
            affiche += F("ACTIfS L.");
        }
        else

            for (byte i = 0; i < nbLayer; i++)
            {
                // déterminer si la layer i est mute
                byte k = ((potVal2 >> i) & B00000001); // le bit de droite est 1 si layer 0 est MUTE ; le 2ème bit est 1 si layer 1 est MUTE, etc...
                if (k == B00000001)
                {
                    affiche += String(i + 1);
                }
                else
                {
                    affiche += (F("-"));
                }
            }

        printRot2(affiche, 16, 300, 3);

        // TODO DEBUG : on doit aussi avoir une valeur qui est ACTIVE LAYERS
    }
    break;

        /////////////////////////////
        // BLACK 08
        /////////////////////////////

    case 142 :
    { // iVlvDelta 
        affiche = afficheValueStraightOrFromSequence(potVal2, "", 0);
        printRot2(affiche, 16, 300, 3);
    }
    break;

        /////////////////////////////
        // BLACK 08
        /////////////////////////////

    case 143:
    { // iVlvDelta
        affiche = afficheValueStraightOrFromSequence(potVal2, "", 0);
        printRot2(affiche, 16, 300, 3);
    }
    break;

        /////////////////////////////
        // BLACK 08
        /////////////////////////////

    case 144:
    { // imidiDouble 
        affiche = afficheValueStraightOrFromSequence(potVal2, "", 0);
        printRot2(affiche, 16, 300, 3);
    }
    break;

    case 145:
    { // iShiftDelta
        affiche = afficheValueStraightOrFromSequence(potVal2, "", 0);
        printRot2(affiche, 16, 300, 3);
    }
    break;

    case 146:
    { //  ishiftDuree
        affiche = afficheValueStraightOrFromSequence(potVal2, "", 0);
        printRot2(affiche, 16, 300, 3);
    }
    break;
    case 147:
    { // iDureeMask 
        affiche = afficheValueStraightOrFromSequence(potVal2, "", 0);
        printRot2(affiche, 16, 300, 3);
    }
    break;
    case 148:
    { // iMask2 
        affiche = afficheValueStraightOrFromSequence(potVal2, "", 0);
        printRot2(affiche, 16, 300, 3);
    }
    break;
    case 149:
    { // iCutoffDureeDelta 
        affiche = afficheValueStraightOrFromSequence(potVal2, "", 0);
        printRot2(affiche, 16, 300, 3);
    }
    break;
    case 150 :
    { // iBringToDureeDelta 
        affiche = afficheValueStraightOrFromSequence(potVal2, "", 0);
        printRot2(affiche, 16, 300, 3);
    }
    break;

    /////////////////////////////
    // BLACK 08
    /////////////////////////////
    // /* 2C28 DISMISSED pour %°
    case 151:
    { // NUM VLV to midiSec midi glitch
        // old potVal2 mapping ;
        // old potVal2 mapping ;

        affiche = nulString;
        affiche = afficheValueStraightOrFromSequence(potVal2, "/", 1);
        affiche += String(DenomRatioDeltaToMsec);
        if (potVal2 >= 1 )
        {
        float RatioDeltaToMsecTemp = (float)potVal2 / (float)DenomRatioDeltaToMsec;
        affiche += F(" : ");
        affiche += String(RatioDeltaToMsecTemp, 2);
        }
        printRot2(affiche, 16, 300, 3);
    }
    break;
        // byte NumRatioDeltaToMsec = 4 ;

    case 152:
    { // DENOM VLV to midiSec midi glitch
        // old potVal2 mapping ;
        // old potVal2 mapping ;
        // affiche =  nulString ; ;
        //
        affiche = String(NumRatioDeltaToMsec) + "/" + afficheValueStraightOrFromSequence(potVal2, " ", 1);
        if ( potVal2 > 0 )
        {
        float RatioDeltaToMsecTemp = (float)NumRatioDeltaToMsec / (float)potVal2;
        affiche += F(" : ");
        affiche += String(RatioDeltaToMsecTemp, 2);
        }
        printRot2(affiche, 16, 300, 3);
    }
    break;
        // byte DenomRatioDeltaToMsec = 0 ;

        // NOTE**** il faut aussi penser à un système faisant varier le Ratio en temps réel ( comme le midi player ! )

    case 153:
    { // Create Mask
        // old potVal2 mapping ;
        // old potVal2 mapping ;

        affiche = nulString;
        ;
        affiche = String153;
        if (nowMillis % 1000 < 700)
        {
            affiche += (ChoixString153.substring(potVal2, potVal2 + 1));
        }
        else
        {
            affiche += F("*");
        }
        affiche += (F(" "));
        printRot2(affiche, 16, 300, 3);

        // NOTE**** trouver une fc réutilisable, du style : DisplayString (  &String153, &ChoixString153, potVal2 )
    }
    break;

    case 156:
    { // choix du Swing
        // old potVal2 mapping ;
        // old potVal2 mapping ;

        affiche = nulString;
        ;
        affiche += (preset156[potVal2]);
        affiche += (F(" "));
        printRot2(affiche, 16, 300, 3);

        // NOTE**** trouver une fc réutilisable, du style : DisplayString (  &String153, &ChoixString153, potVal2 )
    }
    break;

        // case 157 : NameTransfo = F("157 Fuse"); break ;
        // case 158 : NameTransfo = F("158 >Type Fuse"); break ;

    case 158: // Define Type of Fuse
    {
        // old potVal2 mapping ;
        // old potVal2 mapping ;
        affiche = nulString;
        ;
        // 158 Define TypeFuse
        // 1 = Same Note
        // 2 = All Notes
        // 3? = même note à travers octaves ?
        switch (potVal2)
        {
        case 0:
            affiche = (F("1.Same Note"));
            break;
        case 1:
            affiche = (F("2.All Notes"));
            break;
        default:
            affiche = (F("Ugh?"));
            break;
        }
        printRot2(affiche, 16, 300, 3);
    }
    break;

        // case 159 : {
        //     // printRotFast (F("Custom Swing Pattern") );
        //     // old potVal2 mapping ;
        //     // old potVal2 mapping ;
        //
        //     // affiche =  nulString ; ;
        //     // affiche = String153;
        //     // affiche += (ChoixString153.substring(potVal2, potVal2+1)) ;
        //     // affiche += (F(" "));
        //     // printRot2(affiche,16,300,3);
        //
        //
        //     affiche =  nulString ; ;
        //     affiche = String159;
        //     affiche += (ChoixString156.substring(potVal2, potVal2+1)) ;
        //     affiche += (F(" "));
        //     printRot2(affiche,16,300,3);
        //
        //     // affiche =  nulString ; ;
        //     // affiche = (patternSwingCustom);
        //     // affiche+= (ChoixString156.substring(potVal2, potVal2+1)) ;
        //     // affiche+= (F(" "));
        //
        //     // printRot2(affiche,16,300,3);
        //     // preset156[taillePresetString156] = String159 ; // remplace le dernier pattern de la liste par le custom !
        //     // NOTE**** trouver une fc réutilisable, du style : DisplayString (  &String153, &ChoixString153, potVal2 )
        //
        // }
        // break ;

    case 159:
    { // Create Custom Swing pattern

        affiche = nulString;
        ;
        affiche = String159;
        if (nowMillis % 1000 < 700)
        {
            affiche += (ChoixString156.substring(potVal2, potVal2 + 1));
        }
        else
        {
            affiche += F("*");
        }
        affiche += (F(" "));
        printRot2(affiche, 16, 300, 3);

        // NOTE**** trouver une fc réutilisable, du style : DisplayString (  &String153, &ChoixString153, potVal2 )
    }
    break;

    case 162:
    { // Select fc spéciales MidiMatrix Redirect
        //GetNameTransformation(Transfo[counter  - 1][0]);
        //printRotFast (NameTransfo );
        // old potVal2 mapping ;
        // old potVal2 mapping ;
        affiche = nulString;
        ;

        switch (potVal2)
        {
        case 1:
            affiche = (F("1.Empty matrix"));
            break;
        case 2:
            affiche = F("2.CH");
            affiche += flechedroite;
            affiche += F("CHorigine");
            break;
        case 3:
            affiche = F("3.Random 1");
            break;
        case 4:
            affiche = F("4.All");
            affiche += flechedroite;
            affiche += F("CH tget");
            break;
        case 5:
            affiche = F("5.CH tget");
            affiche += flechedroite;
            affiche += F("All");
            break;
        case 6:
            affiche = F("6.All");
            affiche += flechedroite;
            affiche += F("4 first");
            break;
        case 7:
            affiche = F("7.Random ");
            break;
        default:
            affiche = F("Ugh?");
            break;
        }
        printRot2(affiche, 16, 300, 3);
    }
    break;

    case 163:
    { // view Channel direction
        // GetNameTransformation(Transfo[counter  - 1][0]);
        // NameTransfo = "CH" + String(potVal2+1) + NameTransfo ;
        // printRot2(NameTransfo,10,400,2);
        // old potVal2 mapping ;
        // old potVal2 mapping ;
        buffer_and_HARD_setCursor(0, 1);
        printMatrixLine(midiRedirect, potVal2 - 1);
        // MODIF 1C86
        // TODO : transformer en fonction qui donne un String DEBUG ****
    }
    break;

    case 164:
    { // Skip Chunck Parallel Midi Player
        printRot2((SkipChunck == true) ? F("ON ") : F("OFF"), 16, 300, 3);
    }
    break;

    case 172: // Send CC to TX81Z - début de l'affichage auto ON/OFF
    {
        printRot2(sendCCtoTX81Z == true ? F("ON ") : F("OFF"), 16, 300, 3);
    }
    break;

    case 179:
    {
        // Horizontal Mapping
        affiche = "";
        affiche += (F("("));

        affiche += String(mapHSourceMin);
        affiche += (F(","));
        affiche += String(mapHSourceMax);

        affiche += F(")");
        affiche += flechedroite;
        affiche += F("(");

        affiche += String(mapHTargetMin);
        affiche += (F(","));
        affiche += String(mapHTargetMax);
        affiche += (F(")"));
        printRot2(affiche, 16, 400, 3);
    }
    break;

    case 181: // Define Type of Breathe
    {
        // old potVal2 mapping ;
        // old potVal2 mapping ;
        affiche = nulString;
        ;
        // 158 Define TypeFuse
        // 1 = Same Note
        // 2 = All Notes
        // 3? = même note à travers octaves ?
        switch (potVal2)
        {
        case 0:
            affiche = (F("1.move"));
            break;
        case 1:
            affiche = (F("2.move all"));
            break;
        case 2:
            affiche = (F("3.all+layer"));
            break;
        default:
            affiche = (F("Ugh?"));
            break;
        }
        printRot2(affiche, 16, 400, 3);
    }
    break;

    case 186: // Fregoli-ze cette note
    {

        // on va afficher la valeur : -24 à +24
        // on indique aussi à quelle note cela correspond
        // pour ça on utilise noteToWorkOn + la valeur

        // potVal2 = map(counter2, 0, 1023, Transfo[softwareValueEncoderLeft][1] , Transfo[softwareValueEncoderLeft][2]  ) ;

        affiche = GiveNameOfNote(noteToWorkOn) + giveSign(potVal2) + F(" > ") + GiveNameOfNote(noteToWorkOn + potVal2) + F("(") + GiveFrenchNameOfNote(noteToWorkOn + potVal2) + F(")");

        printRot2(affiche, 16, 400, 3);
    }
    break;

    case 187: // Cotard-ize cette note ( make it silent )
    {

        // on va afficher la valeur : -24 à +24
        // on indique aussi à quelle note cela correspond
        // pour ça on utilise noteToWorkOn + la valeur

        affiche = nulString;
        ;
        affiche = GiveNameOfNote(noteToWorkOn) + F("(") + GiveFrenchNameOfNote(noteToWorkOn + potVal2) + F(") > ");

        if (isSilentSByte(noteRedirect[noteToWorkOn]))
        {
            affiche += F("SILENT");
        }
        else
        {
            affiche += F("sound ");
        }

        printRot2(affiche, 16, 400, 3);

        // printRot2(( isSilentSByte(noteRedirect[noteToWorkOn])==true?"SILENT":"sound ",16,400,3);
    }
    break;

    case 188: // Macro pour Cotard / Fregoli
    {
        // old potVal2 mapping ;
        // old potVal2 mapping ;
        String affiche;

        switch (potVal2)
        {
        case 0:
            affiche = F("1.Reset Note redirection");
            break;
        case 1:
            affiche = F("2.Randomize Notes");
            break;
        case 2:
            affiche = F("3.Kill all flats");
            break;
        case 3:
            affiche = F("4.Kill all naturals");
            break;
        case 4:
            affiche = F("5.Move Up/Down all flats");
            break;
        case 5:
            affiche = F("6.All to ONE");
            break;
        case 6:
            affiche = F("7.All to RndONE");
            break;
        case 7:
            affiche = F("8.All to RndTWO");
            break;
        case 8:
            affiche = F("9.Rnd Silencer");
            break;
        case 9:
            affiche = F("10.Inverter Scale");
            break;
        default:
            affiche = F("Oink!");
            break;
        }

        printRot2(affiche, 16, 400, 3);
    }
    break;

    case 189: // Set Type CC Mod source
    {
        // old potVal2 mapping ;
        // old potVal2 mapping ;

        String affiche;
        affiche = giveStringOfCCMod(currentCCMod);

        switch (potVal2)
        {
        case 0:
            affiche += F("0.vide - WTF ?");
            break;
        case 1:
            affiche += F("1.velocity");
            break;
        case 2:
            affiche += F("2.pitch ");
            break;
        case 3:
            affiche += F("3.note (C,C#,etc)");
            break;
        case 4:
            affiche += F("4.LG note");
            break;
        default:
            affiche += F("Oink!");
            break;
        }

        printRot2(affiche, 16, 400, 3);
    }
    break;

    case 190:
    {
        // Select CCMOd
        String affiche;
        affiche = giveStringOfCCMod(currentCCMod);

        affiche += F(" -> ");
        affiche += String(potVal2 + 1);
        printRot2(affiche, 16, 400, 3);
    }
    break;

    case 195: // Set Borders Behavior
    {
        // old potVal2 mapping ;
        // old potVal2 mapping ;

        String affiche;
        affiche = giveStringOfCCMod(currentCCMod);

        switch (potVal2)
        {
        case 0:
            affiche += F(" 1.limit value");
            break;
        case 1:
            affiche += F(" 2.expand value");
            break;
        case 2:
            affiche += F(" 3.no CC send beyond");
            break;
        case 3:
            affiche += F(" 4.middle void");
            break;
        default:
            affiche += F(" Oink!");
            break;
        }

        printRot2(affiche, 16, 400, 3);
    }
    break;

    case 198:
    { // Define Layers Concernes

        // old potVal2 mapping ;
        // old potVal2 mapping ;

        // NOTE **** problème pour sélectionner ACTIVE LAYERS, comme Transfo 141

        affiche = nulString;
        affiche = giveStringOfCCMod(currentCCMod);
        affiche += F(" ");

        if (potVal2 >= 16)
        {
            affiche += F("ACTIfS L.");
        }
        else
            for (byte i = 0; i < nbLayer; i++)
            {
                // déterminer si la layer i est mute
                byte k = ((potVal2 >> i) & B00000001); // le bit de droite est 1 si layer 0 est MUTE ; le 2ème bit est 1 si layer 1 est MUTE, etc...
                if (k == B00000001)
                {
                    affiche += String(i + 1);
                }
                else
                {
                    affiche += (F("-"));
                }
            }
        printRot2(affiche, 16, 300, 3);
    }
    break;

    case 199: //  ON/OFF pour envoi CC Mod à partir de Midi //
    {
        // pileCCMod* CCModPtr ;
        //
        // CCModPtr = giveNthPtrPileComplete(CCModPointeurInitial, currentCCMod);
        // byte value = (*CCModPtr).CCMod.layerConcerne ;
        byte value = CCModTableau[currentCCMod].layerConcerne;
        value = (value & B10000) >> 4;

        printRot2("dire qqch sur midi", 16, 300, 3); // TODO DEBUG

        // TODO écrire qqch ici sur le send midi !
    }
    break;

    case 200: //  Add CC Mod
    {

        // pileCCMod* CCModPtr ;
        //
        // CCModPtr = giveNthPtrPileComplete(CCModPointeurInitial, currentCCMod);
        // bool actif = (*CCModPtr).CCMod.actif ;
        bool actif = CCModTableau[currentCCMod].actif;

        String affiche;
        affiche = giveStringOfCCMod(currentCCMod);

        if (actif == true)
        {
            affiche += F(" ON");
        }
        else
        {
            affiche += F(" OFF");
        }
        // printRot2(actif==true?F("ON "):F("OFF"),16,300,3);
        printRot2(affiche, 16, 300, 3);
    }
    break;

    case 201:
    { // MIDI THRU ON/OFF
        printRot2(midiThru == true ? F("ON ") : F("OFF"), 16, 300, 3);
    }
    break;

    case 204:
    {
        // affiche info sur prochaine note 0
        // old potVal2 mapping ;
        // old potVal2 mapping ;

        byte i = potVal2;
        byte j = 0;
        unsigned long a = 0;

        a = layerLength[i];
        actualizeTimeToPlay(i, j);

        affiche = nulString;
        // unsigned int taille = mesureTaillePileComplete(pInitial[i]);
        pileNote tempNote;
        tempNote = ZEROgetNoteFromPile(pInitial[i], j);

        affiche += String(a) + F(" ") + String(tempNote.timeToPlayON) + " L" + String(i);
        printRot2(affiche, 16, 300, 3);
    }
    break;

/////////////////////////////
// BLACK 08 
/////////////////////////////

    case  205 : 
    { // dureePole1 
        affiche = afficheValueStraightOrFromSequence(potVal2, "msec", 0);
        printRot2(affiche, 16, 300, 3);
    }
    break;

    case 206:
    { // min Pole1
        affiche = afficheValueStraightOrFromSequence(potVal2, "x", -10);
        printRot2(affiche, 16, 300, 3);
    }
    break;

    case 207:
    { // max Pole1
        affiche = afficheValueStraightOrFromSequence(potVal2, "x", -10);
        printRot2(affiche, 16, 300, 3);
    }
    break;

    case 208:
    { // dureePole2
        affiche = afficheValueStraightOrFromSequence(potVal2, "msec", 0);
        printRot2(affiche, 16, 300, 3);
    }
    break;

    case 209:
    { // min Pole2
        affiche = afficheValueStraightOrFromSequence(potVal2, "x", -10);
        printRot2(affiche, 16, 300, 3);
    }
    break;

    case 210:
    { // max Pole2
        affiche = afficheValueStraightOrFromSequence(potVal2, "x", -10);
        printRot2(affiche, 16, 300, 3);
    }
    break;

    case 211:
    { // freq Pole1 
        affiche = afficheValueStraightOrFromSequence(potVal2, "%",  0);
        printRot2(affiche, 16, 300, 3);
    }
    break;


    case 212:
    {
        printRot2(turnOnBipolarRandom == true ? F("ON ") : F("OFF"), 16, 300, 3);
    }
    break;

    case 213:
    {
        // Vertical Mapping pour Vélocités
        String affiche;

        affiche = (F("("));

        affiche += String(FindLowestVelocityOfActive());
        affiche += (F(","));

        affiche += String(FindHighestVelocityOfActive());
        affiche += F(")");
        affiche += flechedroite;
        affiche += F("(");

        affiche += String(targetVelociteMin);
        affiche += (F(","));
        affiche += String(targetVelociteMax);
        affiche += (F(")"));
        printRot2(affiche, 16, 400, 3);
    }
    break;

    case 216:
    { // POOF
        affiche = nulString;

    affiche = afficheValueStraightOrFromSequence(potVal2, "msec", 0);

        affiche += F("  ");

        if (turnOnPoof == true)
        {
            affiche += (F("ON "));
        }
        else
        {
            affiche += (F("OFF"));
        }

        if (showFract)
        {

            if (firstActiveLayer() != 50) // çàd si aucune layer n'est active
            {
                fraction = closestFraction(potVal2, layerLength[firstActiveLayer()], 16, false);
                if (fraction.imprecision < 0)
                {
                    affiche = affiche + "<";
                }
                if (fraction.imprecision > 0)
                {
                    affiche = affiche + ">";
                }
                if (fraction.imprecision == 0)
                {
                    affiche = affiche + "=";
                }

                affiche = affiche + String(fraction.num);
                affiche = affiche + F("/");
                affiche = affiche + String(fraction.den);
            }
        }

        printRot2(affiche, 16, 400, 3);
    }
    break;

    case 217:
    { // Filter or KILL note

        affiche = nulString;

        if (killingNote == true)
        {
            affiche += (F("ON  "));

            affiche += String(potVal2);
            affiche += F(" ");
            affiche += GiveNameOfNote(potVal2);
            affiche += F("(");
            affiche += GiveFrenchNameOfNote(potVal2);
            affiche += F(") ");

            noteToKill = potVal2;
        }
        else
        {
            affiche += (F("OFF "));
            noteToKill = 0;
        }

        printRot2(affiche, 16, 400, 3);
        // killingNote = true ; // il est invalidé dans le programme principal, de sorte que qd on change de fonction, il revient à false ;
    };
    break;

    case 218:
    {
        // old potVal2 mapping ;
        // old potVal2 mapping ;

        busyWithMIDIAffichage = true;

        // channelForCell est défini par case 219
        // tandis que noteForCell est potVal2

        byte noteForCell = potVal2;

        if (softwareValueEncoderLeft != oldCounterLeft)
        {
            // cela signife qu'on vient de tourner le bouton pour arriver sur Cell
            // on peut donc prendre cette valeur de potVal2 pour savoir si par après elle sera modifiée
            initPotVal2 = potVal2;
            initKick = true;
            consToCons = true; // si premier KIck dans Cell, les consolidated doivent jouer du consolidated
            atLeastOneKick = false;
        }

        // dans version plus élaborée :
        // si NOTE jouée sur pad non consolidée -> joue ce qui est indiqué par l'écran
        // si note jouée sur pad a été consolidée -> joue ce qui remplace cette note ( vérifie dans un array )
        //          SAUF si entre le play sur pad le bouton rotatif droit a été modifié :
        //          modifier ce bouton après avoir joué sur le pad en mode CELL signifie donc qu'on veut changer la valeur
        // qui de l'array :
        // idéalement un pour chaque note [0..127] - en pratique on peut se contenter d'une dizaine de notes je suppose
        // sur le Wave Pad il y en a 1 + 4 + 8 = 13

        byte note(0);
        byte channel(0);
        byte velocity(0);
        affiche = nulString;

        affiche = F("CH");
        affiche += String(lastChannel + 1);
        affiche += F("N");
        affiche += String(lastPad);

        affiche += " ";
        affiche += flechedroite;
        affiche += F(" CH");
        affiche += String(channelOutForCell + 1);
        affiche += F("N");
        affiche += String(noteForCell);
        printRot2(affiche, 16, 400, 3);

        if (MIDI3.read(0))
        {
            channel = MIDI3.getChannel() - 1; // donne le channel, pas le codage du channel ! CH1 = 0 pour machine
            note = MIDI3.getData1();
            velocity = MIDI3.getData2();
            // timenote = millis() ;
        }

        if (note != 0)
        {
            switch (MIDI3.getType())
            {
            case midi::NoteOn:
            {

                // digitalWrite(5, HIGH);

                currentPad = note;
                // printRot2(affiche,16,400,3);

                noteForCellArray = note; // cette valeur est utilisée dans le transform pour enregistrer la valeur
                channelInForCell = lastChannel;

                // TODO DEBUG il faudrait aussi que Cell tienne compte du channel d'où vient la note IN !

                if (initKick == true)
                {
                    lastPad = currentPad;
                    lastChannel = channel;
                    channelInForCell = channel;
                }

                if ((currentPad == lastPad) && (potVal2 != initPotVal2))
                {
                    consToCons = false;
                }

                if ((initKick == true) && (currentPad != lastPad))
                {
                    consToCons = true;
                }

                if (isNoteCellConsolidated(channel, note))
                // refaire fonction avec Channel + note ?
                {
                    byte place = givePlaceInTableauForNoteCellConsolidated(channel, note);
                    PlaynoteOn_(0x90 + tableauCell[place].channelOut, tableauCell[place].noteOut, velocity);

                    PlaynoteOn_(0x80 + tableauCell[place].channelOut, tableauCell[place].noteOut, 0);
                    // 2C02 : à mettre dans la pileOnce ?

                    affiche = F("PLAYING ");
                    affiche += String(place);
                    printRot2(affiche, 16, 400, 3);

                    //                                if (consToCons == true ) {
                    //                                    byte place = givePlac eInTableauForNoteCellConsolidated(note);
                    //                                    PlaynoteOn_(0x90+tableauCell[place][1], tableauCell[place][2], velocity) ;
                    //
                    //                                    PlaynoteOn_(0x80+tableauCell[place][1], tableauCell[place][2], velocity) ;
                    //
                    //                                }
                    //                                else
                    // {
                    //                                    PlaynoteOn_(0x90+channelForCell-1, noteForCell, velocity) ;
                    //
                    //                                    PlaynoteOn_(0x80+channelForCell-1, noteForCell, velocity) ;
                    //
                    //                                }
                }

                else
                {
                    PlaynoteOn_(0x90 + channelOutForCell, noteForCell, velocity);
                    initPotVal2 = potVal2;

                    PlaynoteOn_(0x80 + channelOutForCell, noteForCell, velocity);
                }
                // si note non consolidée -> joue note du potVal2

                // si note consolidée -> si initPotVal2 != potVal2 -> joue note du potVal2
                //
                // si note consolidée -> si initPotVal2 == potVal2 -> joue note consolidée OUT
                //
                // si potVal2 == initPotVal2 ( çàd on n'a pas tourné ) et la note frappée a déjà été consolidée
                // çàd qu'il existe une note dans l'array qui correspond à cette note
                // alors on joue la note OUT consolidée
                //
                // // si potVal2 == initPotVal2 ( çàd on n'a pas tourné ) et la note frappée n'a pas été consolidée
                // çàd qu'il n' existe pas une note dans l'array qui correspond à cette note
                // alors on joue la note OUT correspondant à potVal2
                //
                // si potVal2 != initPotVal2 ( çàd on a tourné ),
                // même si la note frappée a déjà été consolidée
                // on joue la note qui correspond à potVal2  ( idem à dessus )

                // digitalWrite(5, LOW);

                lastPad = currentPad;
                lastChannel = channel;
                initKick = false;
            } // fin du NoteON
            break;

            default:
                break;
            }
        }
    }
    break;

    case 219:
    { // Select Channel OUT pour CELL
    };
    break;

    case 220:
    { // SOFT PASS ON/OFF
        // printRot2(softPass == true ? F("ON ") : F("OFF"), 16, 300, 3);
        affiche = (softPass == true ? F("ON ") : F("OFF ")); // 2C28
                                                             // TODO simplifier les "ON" et "OFF" en 1 seul string pour toute mémoire

        unsigned int taille = mesureTaillePileComplete(pSoftPassRedirect);
        affiche += "sz:";
        affiche += String(taille);
        printRot2(affiche, 16, 300, 3);
    }
    break;

    case 223:
    {
        affiche = "DISMISSED";

        // 2C22 suppression, car inutilie vu le REC IN

        printRot2(affiche, 16, 400, 3);
    };
    break;

    case 224:
    {
        // ADJUST END
        //
        affiche = nulString;

        // old potVal2 mapping ;
        // old potVal2 mapping ;

        if (potVal2 > 0)
        {
            affiche = F("+");
            affiche += String(potVal2) + F(" msec ");
        }
        else
        {
            affiche = String(potVal2);
            affiche += F(" msec ");
        }

        byte iLatestStart(0);
        byte iLatestEnd(0);
        byte iLatestEndCalculated(0);

        unsigned long latestStart(0);
        unsigned long latestEnd(0);
        unsigned long latestEndCalculated(0);

        unsigned long calculatedEnd;

        for (byte i = 0; i < nbLayer; i++)
        {
            if (isLayerActive(i))
            {
                unsigned int taille = mesureTaillePileComplete(pInitial[i]);
                pileNote tempNote;

                for (byte j = 0; j < taille; j++)
                {
                    tempNote = ZEROgetNoteFromPile(pInitial[i], j);

                    if (tempNote.note != 0)
                    {

                        if (tempNote.startNote > latestStart)
                        {
                            latestStart = tempNote.startNote;
                            iLatestStart = i;
                        }

                        if (tempNote.endNote > latestEnd)
                        {
                            latestEnd = tempNote.endNote;
                            iLatestEnd = i;
                        }

                        if (tempNote.startNote > tempNote.endNote)
                        {
                            calculatedEnd = layerLength[i] + tempNote.endNote;
                        }
                        else
                        {
                            calculatedEnd = tempNote.endNote;
                        }

                        if (calculatedEnd > latestEndCalculated)
                        {
                            latestEndCalculated = calculatedEnd;
                            iLatestEndCalculated = i;
                        }
                    }
                }
            };
        };

        // if ( latestEndCalculated < layerLength[iLatestEndCalculated] ) {
        //     latestEndCalculated += layerLength[iLatestEndCalculated]  ;
        //     // ceci est juste nécessaire pour que l'affichage soit cohérent quend le calcul est plus petit que la layer,
        //     // car juste après on déduit de ce nombre la layer ( utile qd plus grand )
        // }

        affiche += F("S:");
        affiche += String(layerLength[iLatestStart] - latestStart) + F(" E:") + String(layerLength[iLatestEnd] - latestEnd) + F(" C:") + String((int)((int)layerLength[iLatestEndCalculated] - (int)latestEndCalculated));

        printRot2(affiche, 16, 400, 3);
    };

    break;

    case 225:
    {
        // ADJUST START
        //
        affiche = nulString;
        ;

        // old potVal2 mapping ;
        // old potVal2 mapping ;

        if (potVal2 > 0)
        {
            affiche = F("+");
            affiche += String(potVal2);
            affiche += F("msec ");
        }
        else
        {
            affiche = String(potVal2);
            affiche += F("msec ");
        }

        // byte mLatestStart (0) ;
        // byte mLatestEnd (0) ;
        // byte mLatestEndCalculated (0) ;

        // unsigned int latestEndCalculated (0);

        unsigned long earliestStart(0);
        unsigned long earliestEnd(0);
        bool foundStart = false;

        for (byte i = 0; i < nbLayer; i++)
        {
            if (isLayerActive(i))
            {
                unsigned int taille = mesureTaillePileComplete(pInitial[i]);
                pileNote tempNote;

                for (byte j = 0; j < taille; j++)
                {
                    tempNote = ZEROgetNoteFromPile(pInitial[i], j);

                    if (tempNote.note != 0)
                    {
                        if (foundStart == false)
                        {
                            earliestStart = tempNote.startNote;
                            earliestEnd = tempNote.endNote;
                            foundStart = true;
                        }

                        if (tempNote.startNote < earliestStart)
                        {
                            earliestStart = tempNote.startNote;
                        }

                        if (tempNote.endNote < earliestEnd)
                        {
                            earliestEnd = tempNote.endNote;
                        }
                    }
                }
            };
        };
        affiche += F("S:");
        affiche += String(earliestStart) + F(" E:") + String(earliestEnd);
        // + " C:" + String(layerLength[i]-latestEndCalculated) ;

        printRot2(affiche, 16, 400, 3);
    };
    break;

    case 226:
    { // Modify Sequence
        affiche = afficheValueStraightOrFromSequence(potVal2, "", floorSeq);
        if (potVal2 >= 0)
        {
            affiche = "+" + affiche;
        }

        affiche = affiche + " > " + giveStringOfSequence(currentSequence);

        printRot2(affiche, 16, 300, 3);
    }
    break;

    case 227:
    { // Delete Sequence
        // old potVal2 mapping ;
        // old potVal2 mapping ;

        affiche = nulString;

        affiche = giveStringOfSequence(potVal2);

        printRot2(affiche, 16, 300, 3);
    }
    break;

    case 228:
    { // Select Sequence
        // old potVal2 mapping ;
        // old potVal2 mapping ;

        affiche = nulString;
        ;
        affiche = giveStringOfSequence(potVal2);
        printRot2(affiche, 16, 300, 3);
    }
    break;

    case 229:
    { // Erase 1 digit from SEquence
        // old potVal2 mapping ;
        // old potVal2 mapping ;

        String affiche;
        affiche = giveStringOfSequence(potVal2);
        printRot2(affiche, 16, 300, 3);
    }
    break;

    case 230:
    { // SET Type de Sequence ( fwd, back, rnd, a-r, jitter, rndfrag )
        // old potVal2 mapping ;
        // old potVal2 mapping ;

        affiche = nulString;
        affiche = giveShortStringOfSequence(currentSequence);

        // const byte modeFWD = 0 ; //
        // const byte modeBACK = 1 ;//
        // const byte modeRANDOM = 2 ;
        // const byte modeALLERRETOUR = 3 ;
        // const byte modeJITTER = 4 ;
        // const byte modeRANDOMFRAG = 5 ;

        switch (potVal2)
        {
        case 0:
            affiche += (F("1.FWD"));
            break;
        case 1:
            affiche += (F("2.BACK"));
            break;
        case 2:
            affiche += (F("3.Random"));
            break;
        case 3:
            affiche += (F("4.Aller-Retour"));
            break;
        case 4:
            affiche += (F("5.Jitter"));
            break;
        case 5:
            affiche += (F("6.Rnd Fragments (Riffs)"));
            break;
        case 6:
            affiche += F("7.progression a->b->c");
            break;
        case 7:
            affiche += F("8.rnd spectum a-b");
            break;
        case 8:
            affiche += F("9.bipolar A *c-d E*f-g H%deA");
            break;
        case 9:
            affiche += F("10.bipolar A B C%deA");
        case 10:
            affiche += F("11.n repeater");
            break;

            // cmt sont encodées les valeurs A B C E F G ???
            // proposition BLACK08
        case 11:
            affiche += F("12.Markov <-A/100 ->B/100 self/100");
            break;

        default:
            affiche += (F("--------- "));
            break;
        }

        printRot2(affiche, 16, 300, 3);
    }
    break;

    case 231:
    { // SET Data for jitter : jitterMinUP
        // old potVal2 mapping ;
        // old potVal2 mapping ;

        affiche = nulString;

        // const byte modeFWD = 0 ; //
        // const byte modeBACK = 1 ;//
        // const byte modeRANDOM = 2 ;
        // const byte modeALLERRETOUR = 3 ;
        // const byte modeJITTER = 4 ;
        // const byte modeRANDOMFRAG = 5 ;

        if (sequence[currentSequence].modeSeq != 4)
        {
            affiche = F("only for Jitter");
        }
        else
        {
            affiche = giveShortStringOfSequence(currentSequence);
            affiche += " +" + String(potVal2);

            // byte jitterMinUP;
            // byte jitterMaxUP;
        }

        printRot2(affiche, 16, 300, 3);
    }
    break;

    case 232:
    { // SET Data for jitter : jitterMaxUP
        // old potVal2 mapping ;
        // old potVal2 mapping ;

        affiche = nulString;

        if (sequence[currentSequence].modeSeq != 4)
        {
            affiche = F("only for Jitter");
        }
        else
        {
            affiche = giveShortStringOfSequence(currentSequence) + " +" + String(potVal2);
        }

        printRot2(affiche, 16, 300, 3);
    }
    break;

    case 233:
    { // SET Data for jitter : jitterMinDOWN
        // old potVal2 mapping ;
        // old potVal2 mapping ;

        affiche = nulString;

        if (sequence[currentSequence].modeSeq != 4)
        {
            affiche = F("only for Jitter");
        }
        else
        {
            affiche = giveShortStringOfSequence(currentSequence) + " +" + String(potVal2);
        }

        printRot2(affiche, 16, 300, 3);
    }
    break;

    case 234:
    { // SET Data for jitter : jitterMaxDOWN
        // old potVal2 mapping ;
        // old potVal2 mapping ;

        affiche = nulString;

        if (sequence[currentSequence].modeSeq != 4)
        {
            affiche = F("only for Jitter");
        }
        else
        {
            affiche = giveShortStringOfSequence(currentSequence) + " +" + String(potVal2);
        }

        printRot2(affiche, 16, 300, 3);
    }
    break;

    case 235:
    { // SET Data for jitter : jitterStaticMin
        // old potVal2 mapping ;
        // old potVal2 mapping ;

        affiche = nulString;

        if (sequence[currentSequence].modeSeq != 4)
        {
            affiche = F("only for Jitter");
        }
        else
        {
            affiche = giveShortStringOfSequence(currentSequence);
            affiche += F(" +");
            affiche += String(potVal2);
        }

        printRot2(affiche, 16, 300, 3);
    }
    break;

    case 236:
    { // SET Data for jitter : jitterStaticMax
        // old potVal2 mapping ;
        // old potVal2 mapping ;

        affiche = nulString;

        if (sequence[currentSequence].modeSeq != 4)
        {
            affiche = F("only for Jitter");
        }
        else
        {
            affiche = giveShortStringOfSequence(currentSequence) + " +" + String(potVal2);
        }

        printRot2(affiche, 16, 300, 3);
    }
    break;

    case 237:
    { // SET Data for RAndom Frag : Size RAndom Fragment
        // old potVal2 mapping ;
        // old potVal2 mapping ;

        affiche = nulString;

        if (sequence[currentSequence].modeSeq != 5)
        {
            affiche = F("only for RndFragments");
        }
        else
        {
            affiche = giveShortStringOfSequence(currentSequence) + " size:" + String(potVal2);
        }

        printRot2(affiche, 16, 300, 3);
    }
    break;

    case 238:
    { // SET Data for RAndom Frag : Nb Repeats
        // old potVal2 mapping ;
        // old potVal2 mapping ;

        affiche = nulString;

        if (sequence[currentSequence].modeSeq != 5)
        {
            affiche = F("only for RndFragments");
        }
        else
        {
            affiche = giveShortStringOfSequence(currentSequence) + " R:" + String(potVal2);
        }

        printRot2(affiche, 16, 300, 3);
    }
    break;

    case 239:
    { // SET ACTION for Sequence
        // old potVal2 mapping ;
        // old potVal2 mapping ;

        affiche = nulString;

        // byte action ; // 00 = CC    1 = NOte     2 = Velocite    plus tard : 3 = SWING
        // // byte type ; // 0 FWD    1 BACK    2 RND    3 A-R    4 JITTER    5 RND-FRG est MODESEQ
        // byte CC ;
        // byte channel ;
        // byte layer ;

        switch (potVal2)
        {
        case 0:
            affiche += (F("1.Pitch ADD")); // DONE
            break;
        case 1:
            affiche += (F("2.Send CC")); // DONE
            break;
        case 2:
            affiche += (F("3.Velocity ADD")); // DONE
            break;
        case 3:
            affiche += (F("4.Pitch SET")); // 2C02
            break;

        case 4:
            affiche += (F("5.Event List"));
            break;
        case 5:
            affiche += (F("6.LG note ADD")); // DONE - HOORIBLE TODO BETTER
            break;
        case 6:
            affiche += (F("7.LayerL SET")); // DONE 2C20
            break;
        case 7:
            affiche += F("8.LayerL ADD"); // DONE 2C20
            break;
        case 8:
            affiche += F("9.LayerL %"); // DONE 2C20
            break;


        case 9:
            affiche += (F("10.Vel SET")); // DONE 2C20 16-2-2020
            break;
        case 10:
            affiche += F("11.Vel ADD"); // DONE 2C20 16-2-2020 , idem à 2  - REDONE ???
            break;
        case 11:
            affiche += F("12.Vel %"); // DONE 2C20 16-2-2020
            break;


        case 12:
            affiche += F("13.NoteL SET"); // DONE
            break;
        case 13:
            affiche += F("14.NoteL ADD"); // DONE 2C20
            break;
        case 14:
            affiche += F("15.NoteL %"); // DONE 2C20
            break;


        case 15:
            affiche += F("16.Degree ADD"); // DONE 2C20 16-2-2020
            break;
        case 16:
            affiche += F("17.Degree RND"); // DONE 2C20 16-2-2020
            break;
        case 17:
            affiche += F("18.Vel RND"); // DONE 2C20 16-2-2020
            break;
        case 18:
            affiche += F("19.Note ON/OFF"); // TODO
            break;
        case 19:
            affiche += F("20.Pitch RND"); // DONE 2C20 16-2-2020
            break;

        case 20:
            affiche += F("21.Set CH"); // BLACK08
            break;
        case 21:
            affiche += F("22.Add CH"); // BLACK08
            break;
case 22:
            affiche += F("23.Bug CH"); // BLACK09 conserve un bug entre notes et CH 
            break;
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
